100prznt/Temp2IoT/docu/ColorSchemes.png

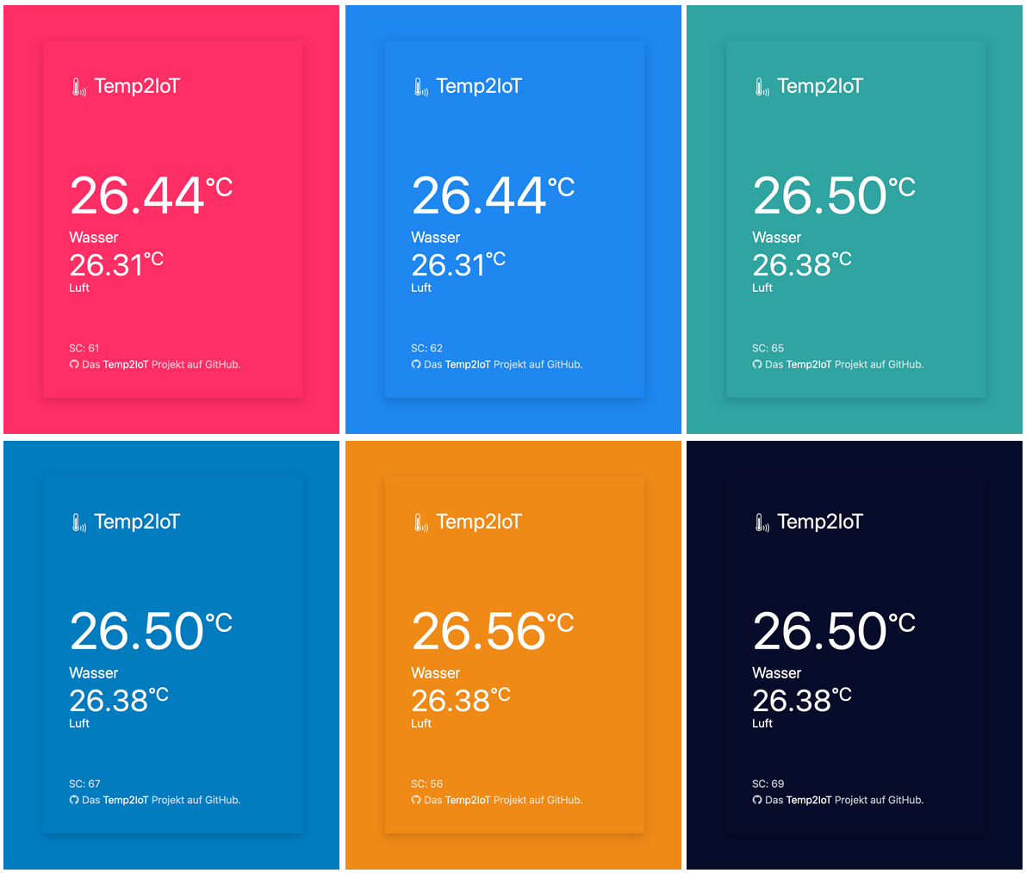
docu/ColorSchemes.png
