100prznt/Temp2IoT/docu/dev_view_v2.jpg

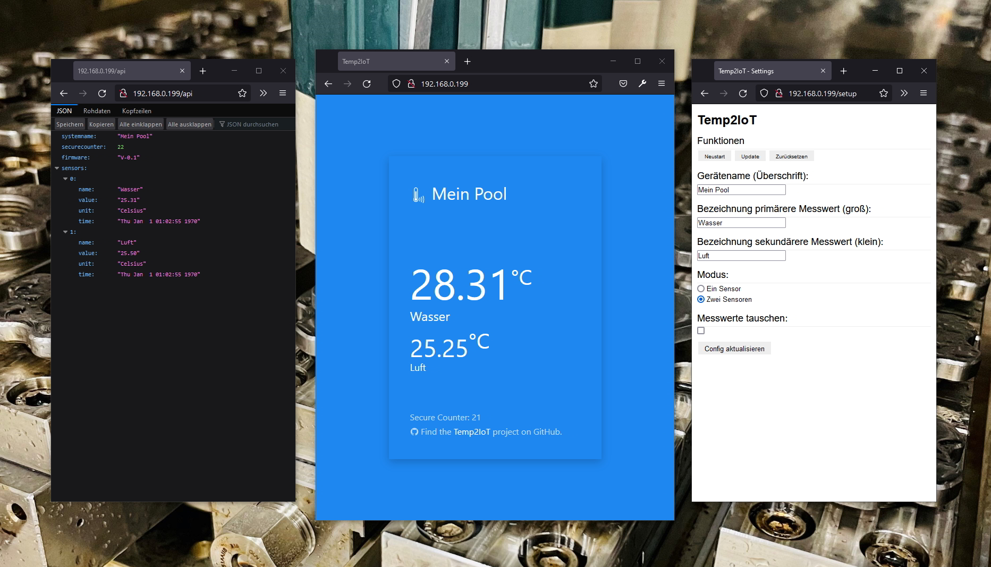
docu/dev_view_v2.jpg
