100prznt/Temp2IoT/docu/ide_preferences.png

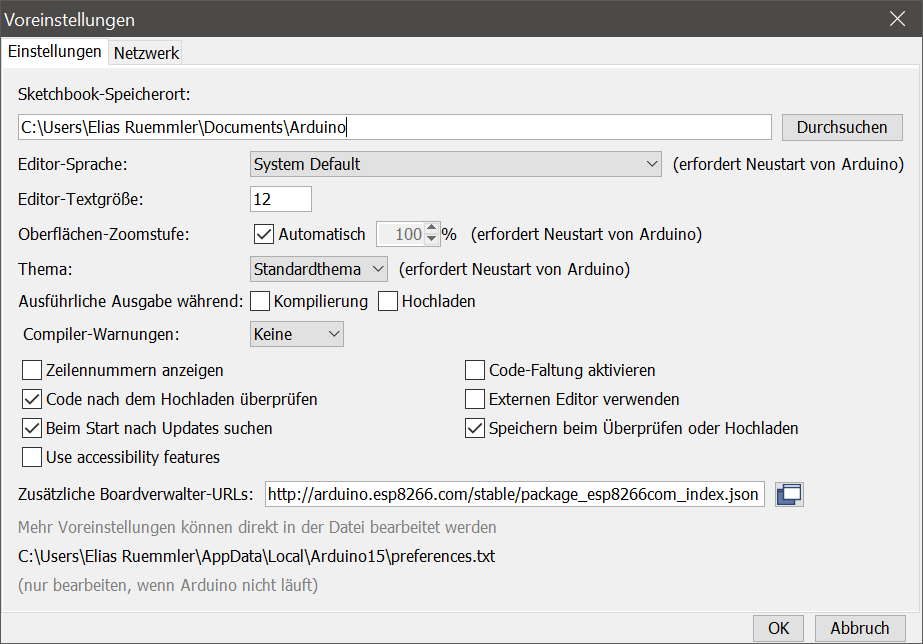
docu/ide_preferences.png
