100prznt/Temp2IoT/docu/IMG_1799.jpg

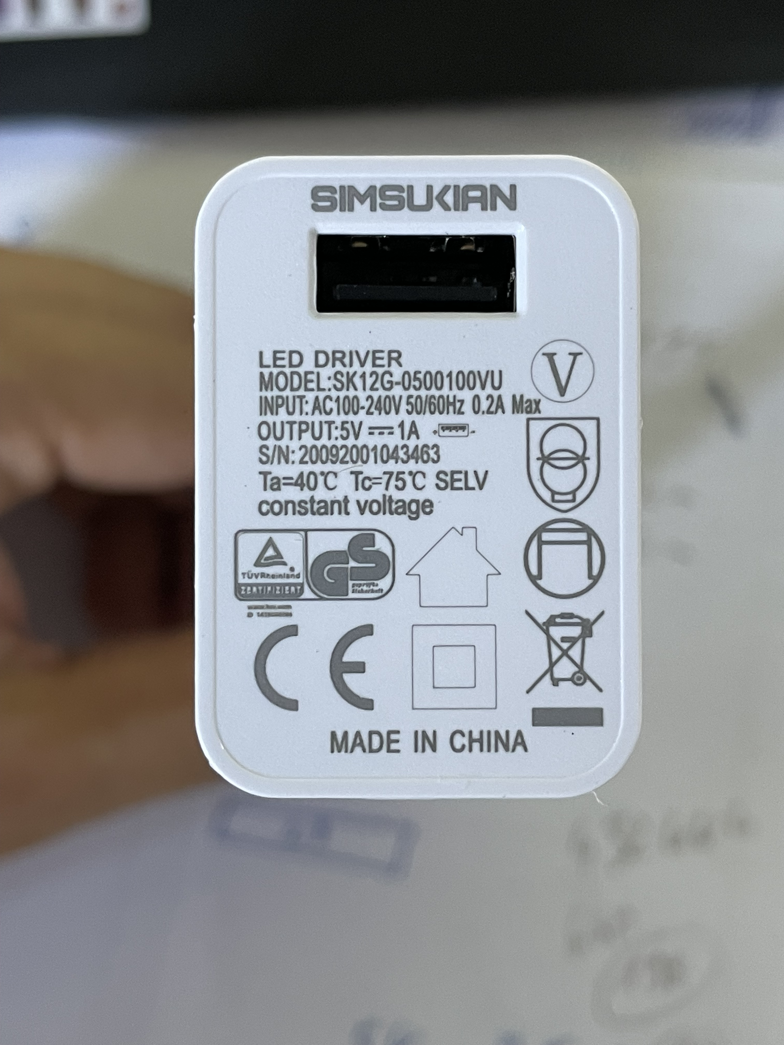
docu/IMG_1799.jpg
