100prznt/Temp2IoT/docu/iobroker_object.png

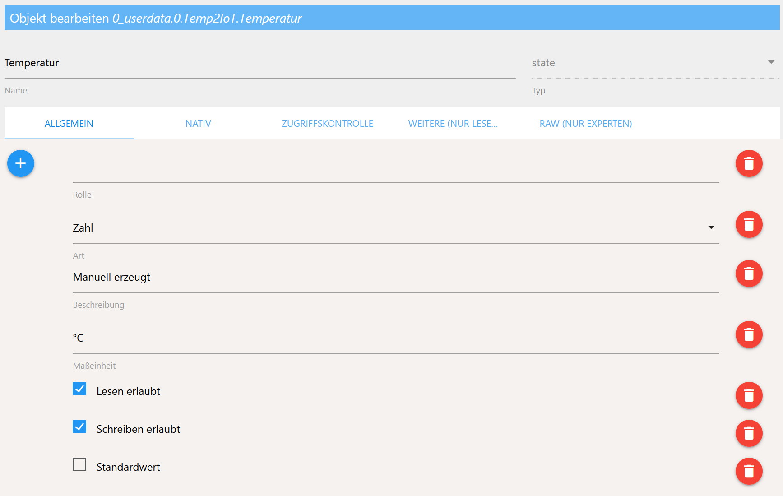
docu/iobroker_object.png
