100prznt/Temp2IoT/docu/iobroker_script.png

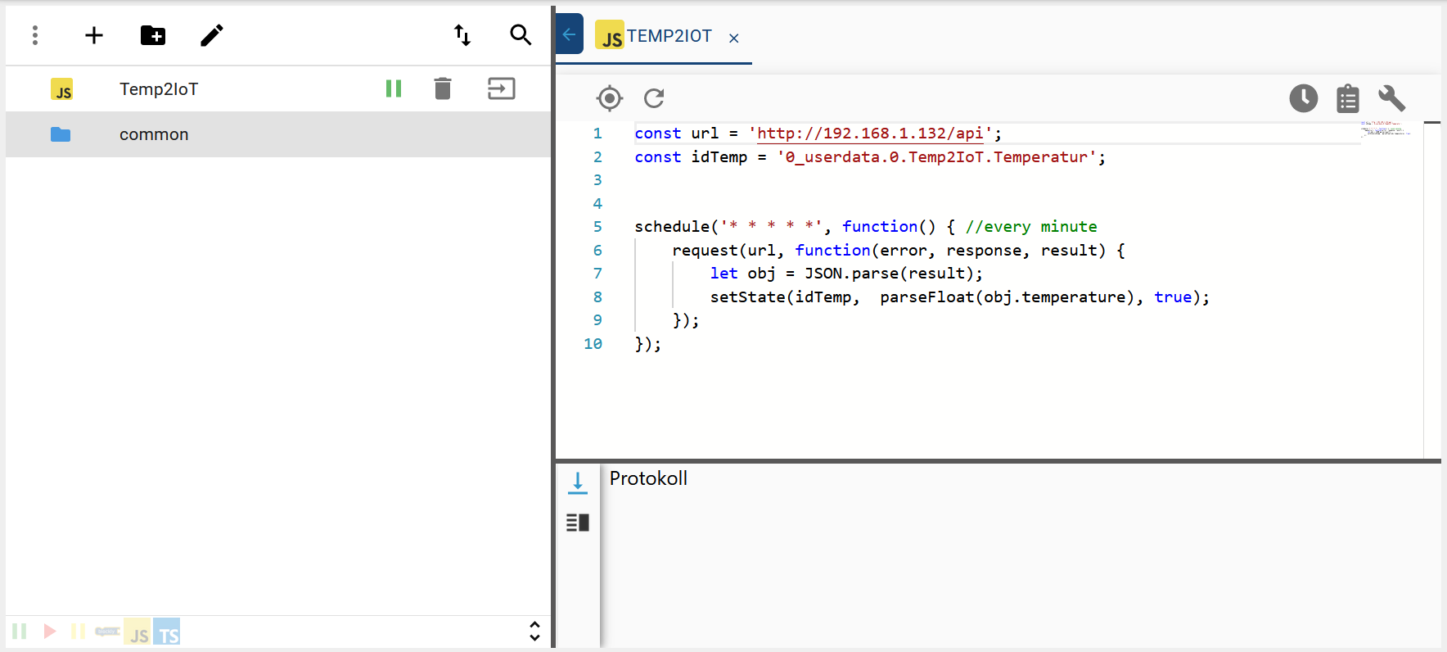
docu/iobroker_script.png
