100prznt/Temp2IoT/docu/RingBuffer_Scheme.PNG

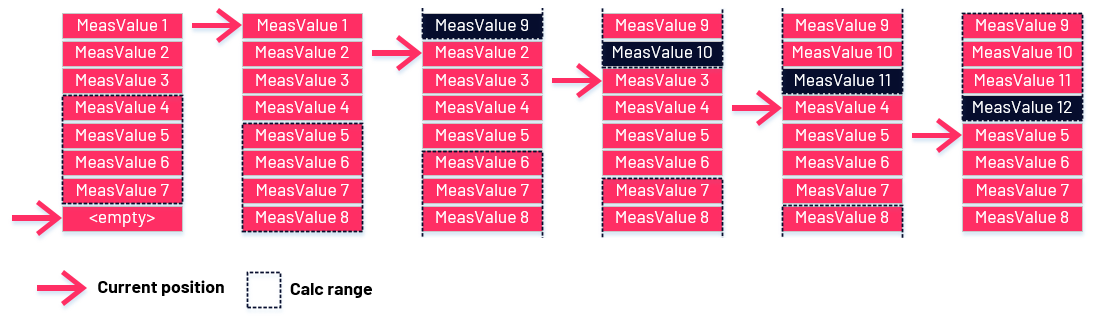
docu/RingBuffer_Scheme.PNG
