100prznt/Temp2IoT/hardware/temp2iot_wiring.png

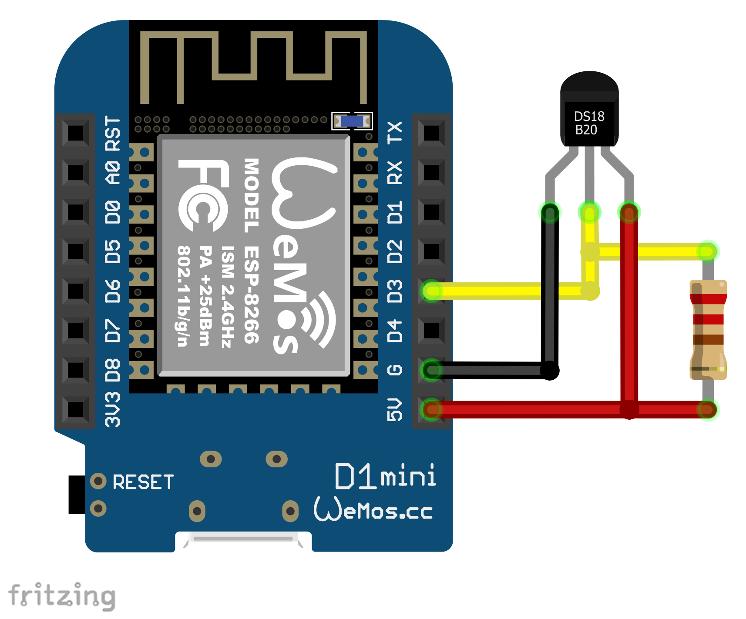
hardware/temp2iot_wiring.png
