100prznt/Temp2IoT/docu/debug-output.png

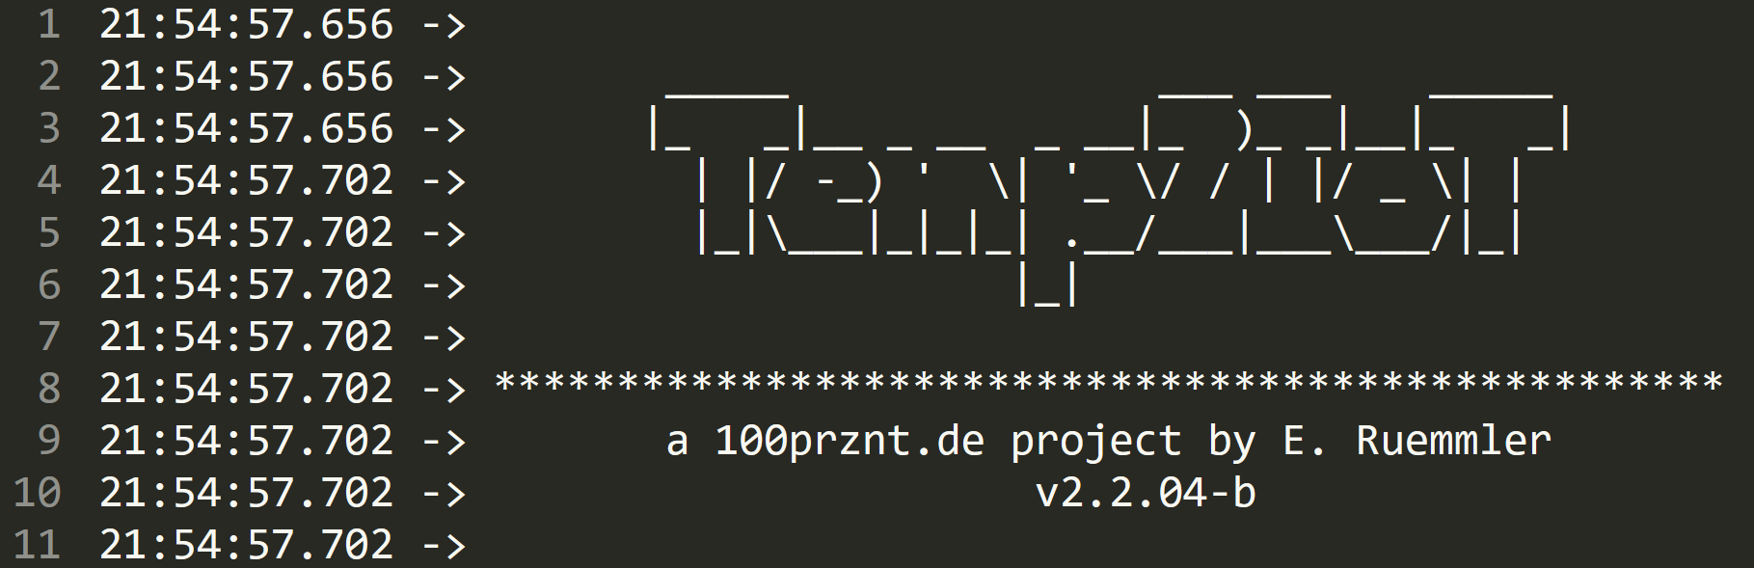
docu/debug-output.png
